Saroja-J/ESP32-Board-/2_layer PCB/Images/Bottom_view.png

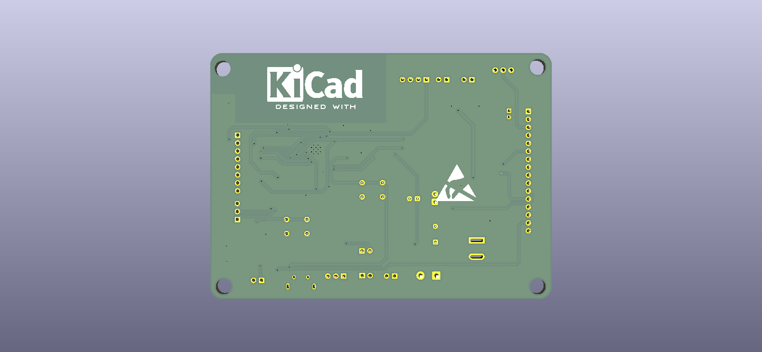
2_layer PCB/Images/Bottom_view.png
