Saroja-J/ESP32-Board-/2_layer PCB/Images/Img2.png

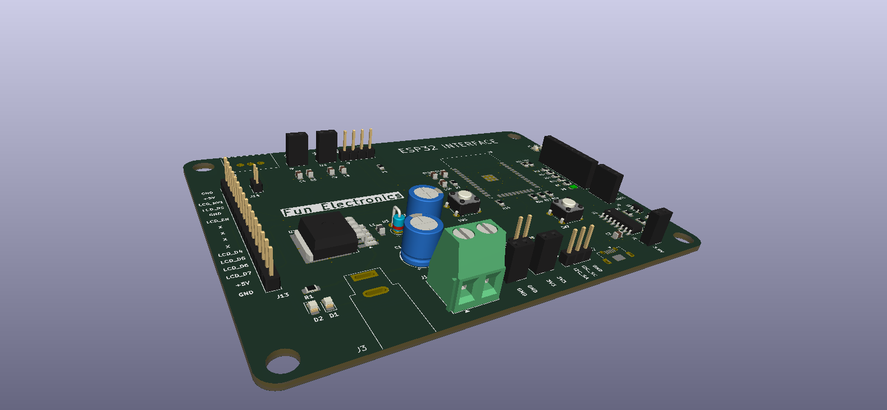
2_layer PCB/Images/Img2.png
