Saroja-J/ESP32-Board-/2_layer PCB/Images/Img.png

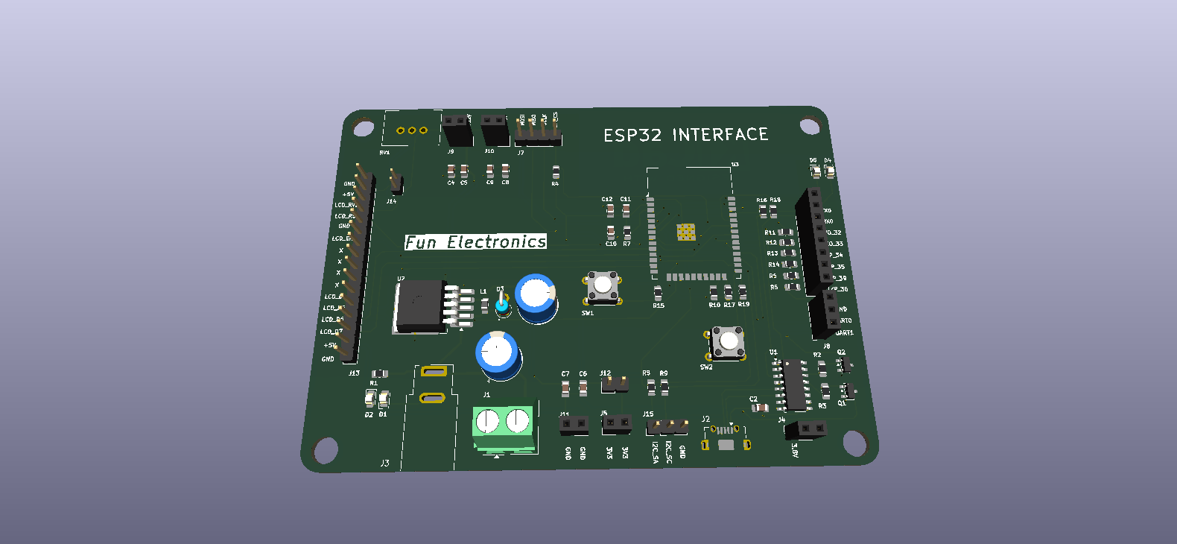
2_layer PCB/Images/Img.png
