Saroja-J/ESP32-Board-/2_layer PCB/Images/layout.png

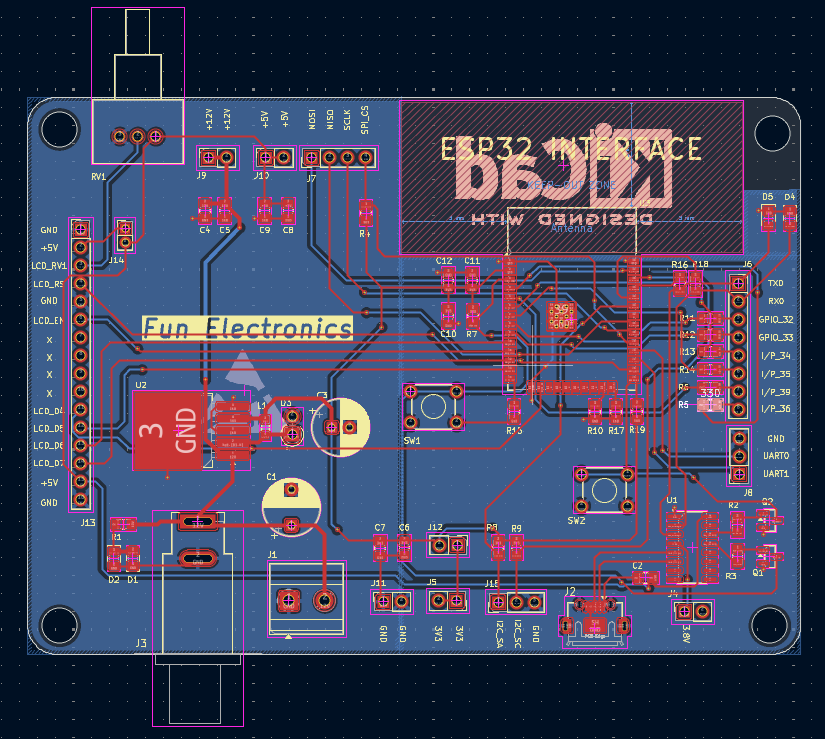
2_layer PCB/Images/layout.png
