Saroja-J/ESP32-Board-/4_Layer PCB/Images/img.png

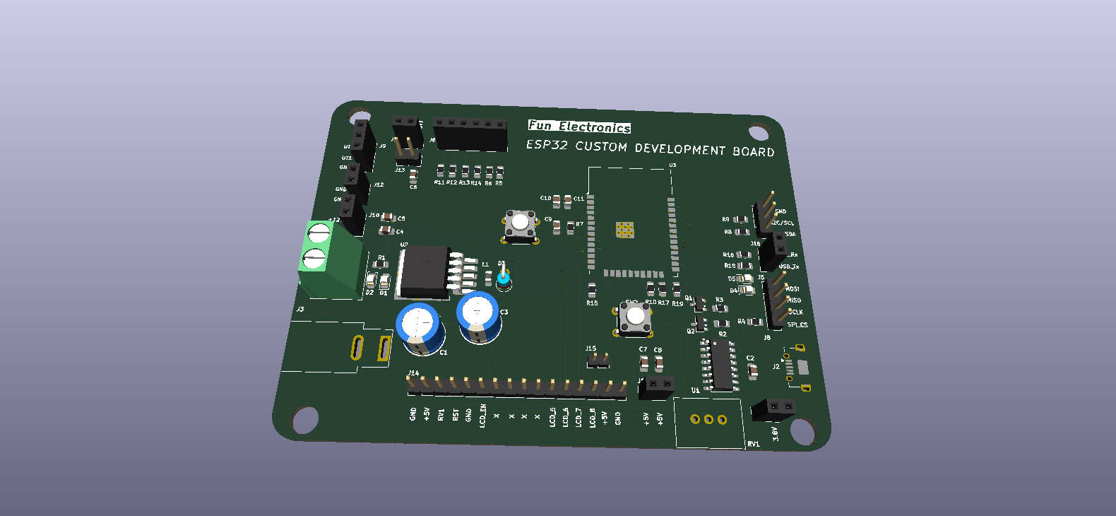
4_Layer PCB/Images/img.png
