Saroja-J/ESP32-Board-/4_Layer PCB/Images/layout_#.png

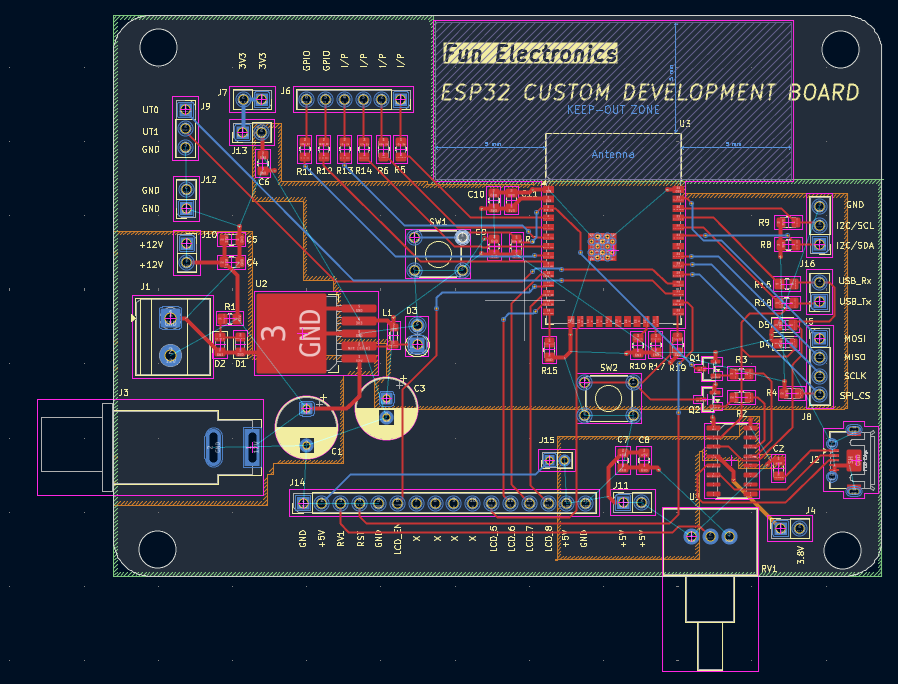
4_Layer PCB/Images/layout_#.png
